TXWD1234/LogicalRedstone/components/redstone-dust/CAD/piece/Redstone Dust - Center.stl

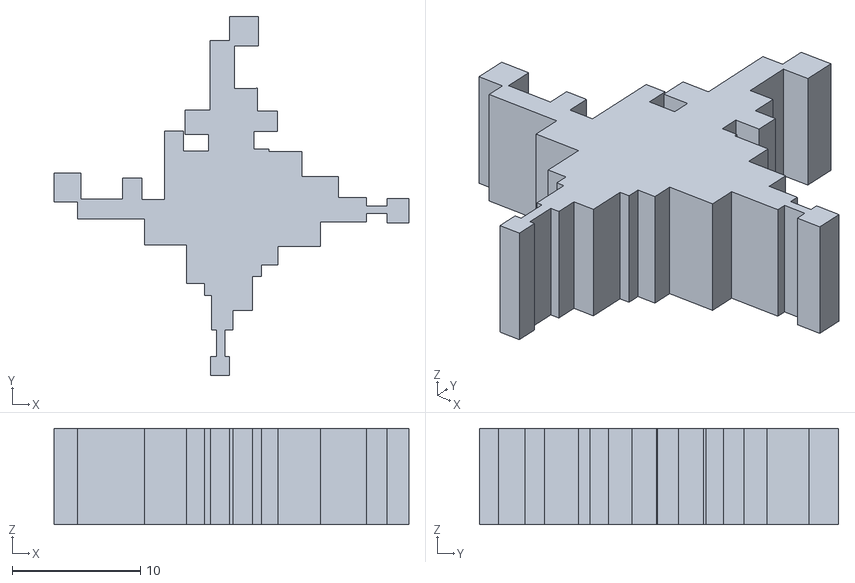
[picture p18: CAD file, 2026-07-06]
components/redstone-dust/CAD/piece/Redstone Dust - Center.stl
27.6 x 28.0 x 7.50
