TXWD1234/LogicalRedstone/components/redstone-button/schematics/redstone-button.kicad_sch

## KiCad design components/redstone-button/schematics/redstone-button.kicad_sch (2026-07-06)

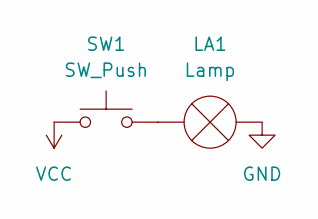
[picture p21: schematic redstone-button.kicad_sch]

Parts:
LA1: Lamp
SW1: SW_Push

Connections:
GND: LA1.1 (-)
unnamed: LA1.2 (+), SW1.2
VCC: SW1.1
