TXWD1234/LogicalRedstone/components/redstone-dust/schematics/redstone-dust-corner.kicad_sch

## KiCad design components/redstone-dust/schematics/redstone-dust-corner.kicad_sch (2026-07-06)

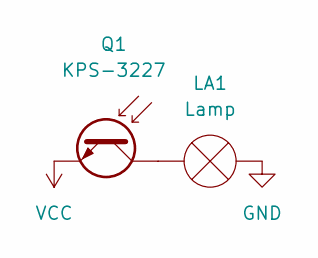
[picture p22: schematic redstone-dust-corner.kicad_sch]

Parts:
LA1: Lamp
Q1: KPS-3227; Kingbright_KPS-3227

Connections:
GND: LA1.1 (-)
unnamed: LA1.2 (+), Q1.1, Q1.3
VCC: Q1.2, Q1.4
