TXWD1234/LogicalRedstone/components/redstone-dust/schematics/redstone-dust-t-junction.kicad_sch

## KiCad design components/redstone-dust/schematics/redstone-dust-t-junction.kicad_sch (2026-07-06)

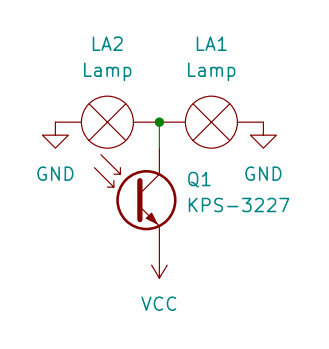
[picture p23: schematic redstone-dust-t-junction.kicad_sch]

Parts:
LA1, LA2: Lamp
Q1: KPS-3227; Kingbright_KPS-3227

Connections:
GND: LA1.1 (-), LA2.1 (-)
unnamed: LA1.2 (+), LA2.2 (+), Q1.1, Q1.3
VCC: Q1.2, Q1.4
