TXWD1234/LogicalRedstone/components/redstone-repeater/schematics/redstone-repeater.kicad_sch

## KiCad design components/redstone-repeater/schematics/redstone-repeater.kicad_sch (2026-07-06)

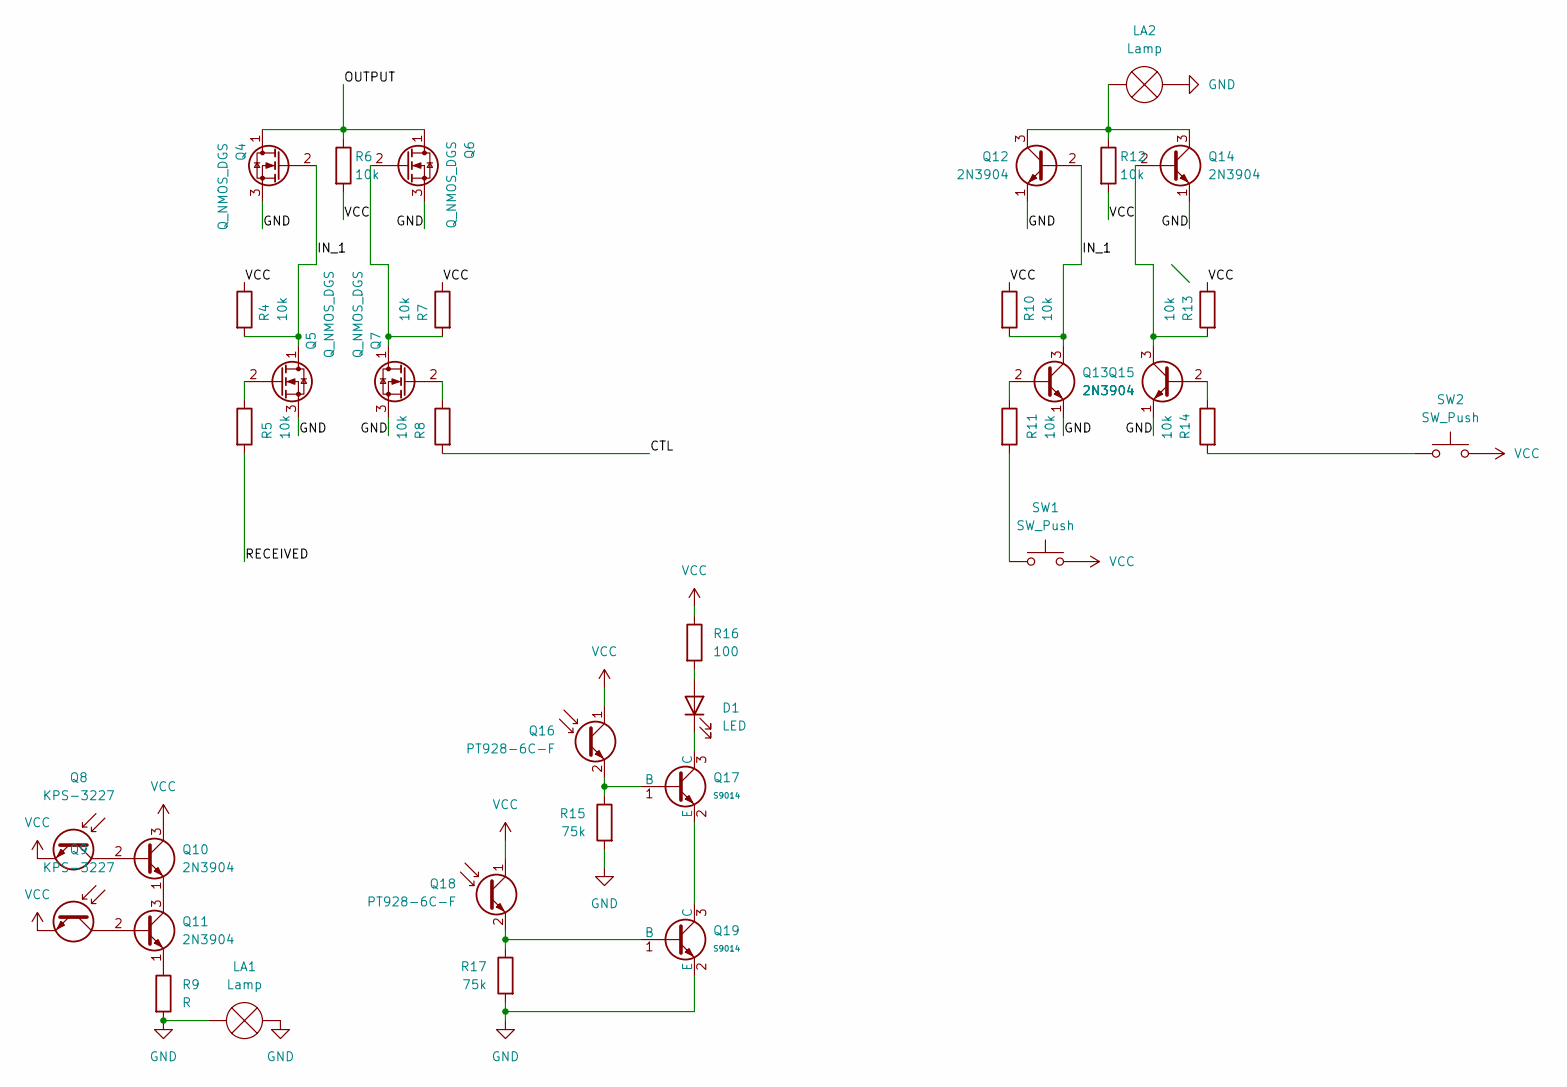
[picture p24: schematic redstone-repeater.kicad_sch]

Parts:
D1: LED
LA1, LA2: Lamp
Q4, Q5, Q6, Q7: Q_NMOS_DGS
Q8, Q9: KPS-3227; Kingbright_KPS-3227
Q10, Q11, Q12, Q13, Q14, Q15: 2N3904; TO-92_Inline
Q16, Q18: PT928-6C-F
Q17, Q19: S9014; Q_SOT-23; Part S9014; LCSC C20069130
R4, R5, R7, R8, R10, R11, R13, R14: 10k; R_Axial_DIN0207_L6.3mm_D2.5mm_P7.62mm_Horizontal
R6, R12: 10k
R9: R
R15, R17: 75k
R16: 100
SW1, SW2: SW_Push

Connections:
CTL: R8.2
GND: LA1.1 (-), LA1.2 (+), LA2.1 (-), Q4.3 (S), Q5.3 (S), Q6.3 (S), Q7.3 (S), Q12.1 (E), Q13.1 (E), Q14.1 (E), Q15.1 (E), Q19.2 (E), R9.2, R15.2, R17.2
IN_1: Q4.2 (G), Q5.1 (D), Q12.2 (B), Q13.3 (C), R4.2, R10.2
unnamed: D1.1 (K), Q17.3 (C)
unnamed: D1.2 (A), R16.2
unnamed: LA2.2 (+), Q12.3 (C), Q14.3 (C), R12.1
unnamed: Q5.2 (G), R5.1
unnamed: Q6.2 (G), Q7.1 (D), R7.2
unnamed: Q7.2 (G), R8.1
unnamed: Q10.1 (E), Q11.3 (C)
unnamed: Q8.1, Q8.3, Q10.2 (B)
unnamed: Q11.1 (E), R9.1
unnamed: Q9.1, Q9.3, Q11.2 (B)
unnamed: Q13.2 (B), R11.1
unnamed: Q14.2 (B), Q15.3 (C), R13.2
unnamed: Q15.2 (B), R14.1
unnamed: Q16.2 (E), Q17.1 (B), R15.1
unnamed: Q17.2 (E), Q19.3 (C)
unnamed: Q18.2 (E), Q19.1 (B), R17.1
unnamed: R11.2, SW1.1
unnamed: R14.2, SW2.1
OUTPUT: Q4.1 (D), Q6.1 (D), R6.1
RECEIVED: R5.2
VCC: Q8.2, Q8.4, Q9.2, Q9.4, Q10.3 (C), Q16.1 (C), Q18.1 (C), R4.1, R6.2, R7.1, R10.1, R12.2, R13.1, R16.1, SW1.2, SW2.2
