TXWD1234/LogicalRedstone/components/redstone-torch/schematics/redstone-torch.kicad_sch

## KiCad design components/redstone-torch/schematics/redstone-torch.kicad_sch (2026-07-06)

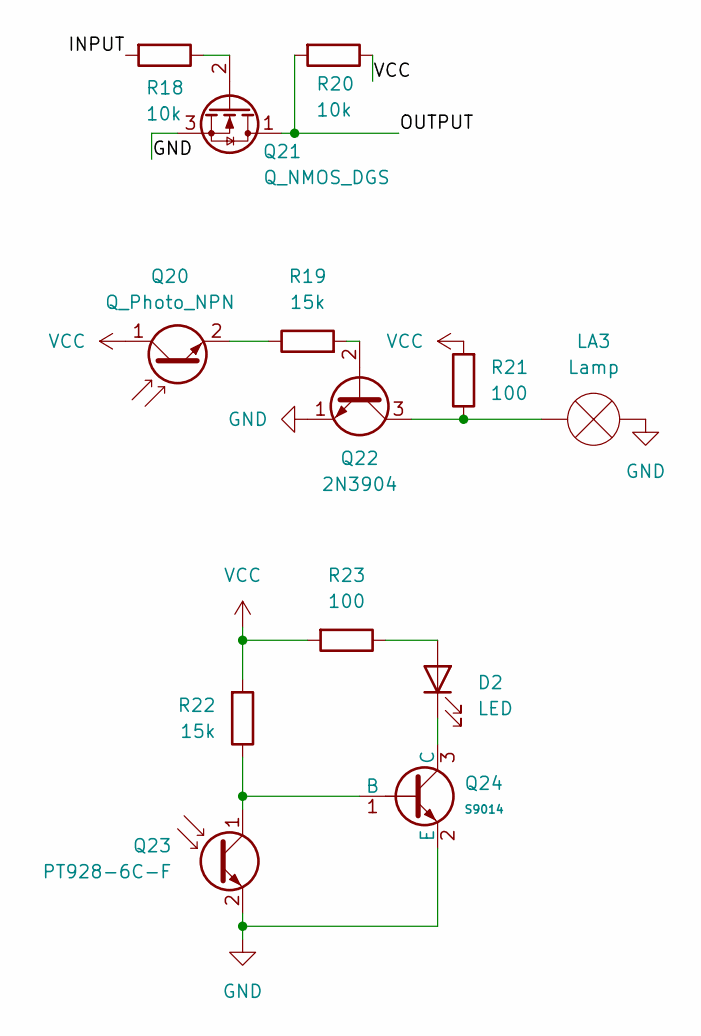
[picture p25: schematic redstone-torch.kicad_sch]

Parts:
D2: LED
LA3: Lamp
Q20: Q_Photo_NPN
Q21: Q_NMOS_DGS
Q22: 2N3904; TO-92_Inline
Q23: PT928-6C-F
Q24: S9014; Q_SOT-23; Part S9014; LCSC C20069130
R18, R20: 10k; R_Axial_DIN0207_L6.3mm_D2.5mm_P7.62mm_Horizontal
R19, R22: 15k
R21, R23: 100

Connections:
GND: LA3.1 (-), Q21.3 (S), Q22.1 (E), Q23.2 (E), Q24.2 (E)
INPUT: R18.2
unnamed: D2.1 (K), Q24.3 (C)
unnamed: D2.2 (A), R23.1
unnamed: LA3.2 (+), Q22.3 (C), R21.1
unnamed: Q20.2 (E), R19.1
unnamed: Q21.2 (G), R18.1
unnamed: Q22.2 (B), R19.2
unnamed: Q23.1 (C), Q24.1 (B), R22.1
OUTPUT: Q21.1 (D), R20.2
VCC: Q20.1 (C), R20.1, R21.2, R22.2, R23.2
