TXWD1234/LogicalRedstone/components/spec/redstone-repeater/redstone-repeater.kicad_sch

## KiCad design components/spec/redstone-repeater/redstone-repeater.kicad_sch (2026-07-05)

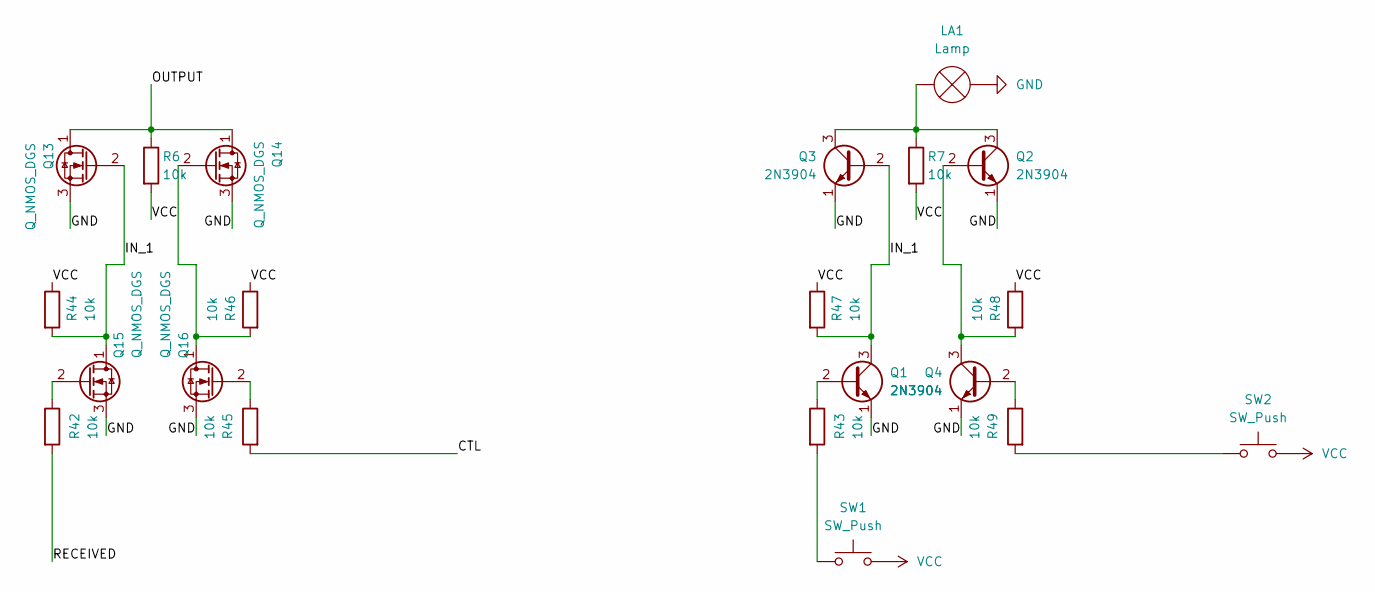
[picture p26: schematic redstone-repeater.kicad_sch]

Parts:
LA1: Lamp
Q1, Q2, Q3, Q4: 2N3904; TO-92_Inline
Q13, Q14, Q15, Q16: Q_NMOS_DGS
R6, R7: 10k
R42, R43, R44, R45, R46, R47, R48, R49: 10k; R_Axial_DIN0207_L6.3mm_D2.5mm_P7.62mm_Horizontal
SW1, SW2: SW_Push

Connections:
CTL: R45.2
GND: LA1.1 (-), Q1.1 (E), Q2.1 (E), Q3.1 (E), Q4.1 (E), Q13.3 (S), Q14.3 (S), Q15.3 (S), Q16.3 (S)
IN_1: Q1.3 (C), Q3.2 (B), Q13.2 (G), Q15.1 (D), R44.2, R47.2
unnamed: LA1.2 (+), Q2.3 (C), Q3.3 (C), R7.1
unnamed: Q1.2 (B), R43.1
unnamed: Q2.2 (B), Q4.3 (C), R48.2
unnamed: Q4.2 (B), R49.1
unnamed: Q14.2 (G), Q16.1 (D), R46.2
unnamed: Q15.2 (G), R42.1
unnamed: Q16.2 (G), R45.1
unnamed: R43.2, SW1.1
unnamed: R49.2, SW2.1
OUTPUT: Q13.1 (D), Q14.1 (D), R6.1
RECEIVED: R42.2
VCC: R6.2, R7.2, R44.1, R46.1, R47.1, R48.1, SW1.2, SW2.2
