TXWD1234/LogicalRedstone/components/spec/redstone-torch/redstone-torch.kicad_sch

## KiCad design components/spec/redstone-torch/redstone-torch.kicad_sch (2026-07-05)

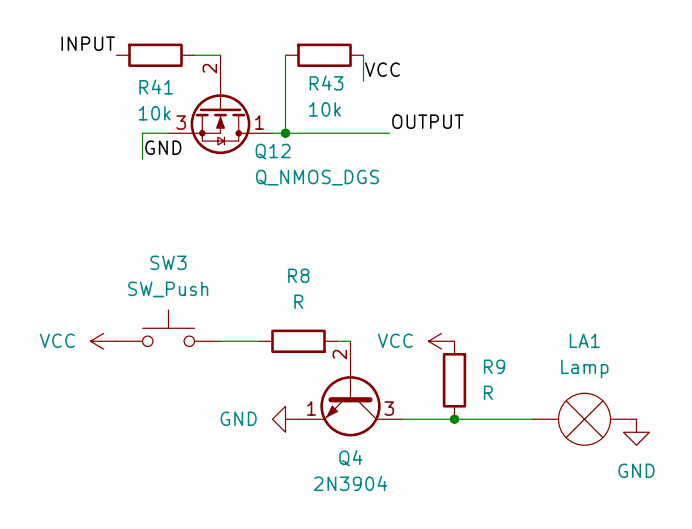
[picture p27: schematic redstone-torch.kicad_sch]

Parts:
LA1: Lamp
Q4: 2N3904; TO-92_Inline
Q12: Q_NMOS_DGS
R8, R9: R
R41, R43: 10k; R_Axial_DIN0207_L6.3mm_D2.5mm_P7.62mm_Horizontal
SW3: SW_Push

Connections:
GND: LA1.1 (-), Q4.1 (E), Q12.3 (S)
INPUT: R41.2
unnamed: LA1.2 (+), Q4.3 (C), R9.1
unnamed: Q4.2 (B), R8.2
unnamed: Q12.2 (G), R41.1
unnamed: R8.1, SW3.2
OUTPUT: Q12.1 (D), R43.2
VCC: R9.2, R43.1, SW3.1
