TXWD1234/LogicalRedstone/demo/adder/schematics/full-adder.kicad_sch

## KiCad design demo/adder/schematics/full-adder.kicad_sch (2026-07-05)

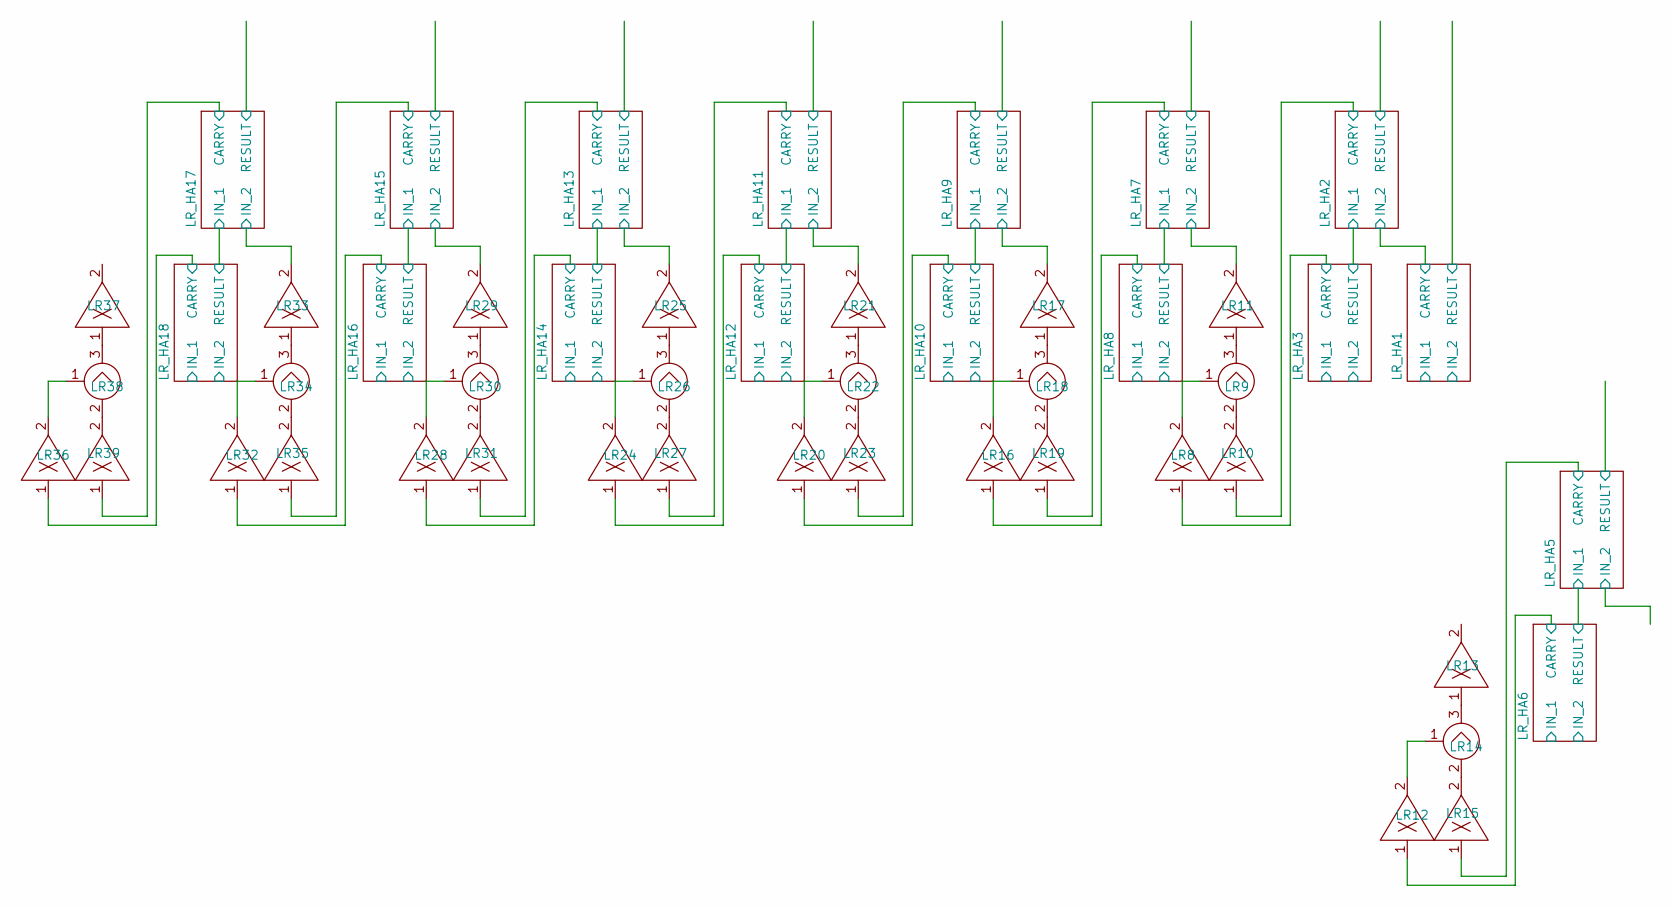
[picture p28: schematic full-adder.kicad_sch]

Parts:
LR8, LR9, LR10, LR11, LR12, LR13, LR14, LR15, LR16, LR17, LR18, LR19, LR20, LR21, LR22, LR23, LR24, LR25, LR26, LR27, LR28, LR29, LR30, LR31, LR32, LR33, LR34, LR35, LR36, LR37, LR38, LR39: (no value)

Connections:
CARRY: LR8.1, LR10.1, LR12.1, LR15.1, LR16.1, LR19.1, LR20.1, LR23.1, LR24.1, LR27.1, LR28.1, LR31.1, LR32.1, LR35.1, LR36.1, LR39.1
IN_2: LR11.2, LR17.2, LR21.2, LR25.2, LR29.2, LR33.2
unnamed: LR8.2, LR9.1
unnamed: LR9.2, LR10.2
unnamed: LR9.3, LR11.1
unnamed: LR12.2, LR14.1
unnamed: LR13.1, LR14.3
unnamed: LR14.2, LR15.2
unnamed: LR16.2, LR18.1
unnamed: LR17.1, LR18.3
unnamed: LR18.2, LR19.2
unnamed: LR20.2, LR22.1
unnamed: LR21.1, LR22.3
unnamed: LR22.2, LR23.2
unnamed: LR24.2, LR26.1
unnamed: LR25.1, LR26.3
unnamed: LR26.2, LR27.2
unnamed: LR28.2, LR30.1
unnamed: LR29.1, LR30.3
unnamed: LR30.2, LR31.2
unnamed: LR32.2, LR34.1
unnamed: LR33.1, LR34.3
unnamed: LR34.2, LR35.2
unnamed: LR36.2, LR38.1
unnamed: LR37.1, LR38.3
unnamed: LR38.2, LR39.2
