TXWD1234/LogicalRedstone/demo/adder/schematics/half-adder.kicad_sch

## KiCad design demo/adder/schematics/half-adder.kicad_sch (2026-07-05)

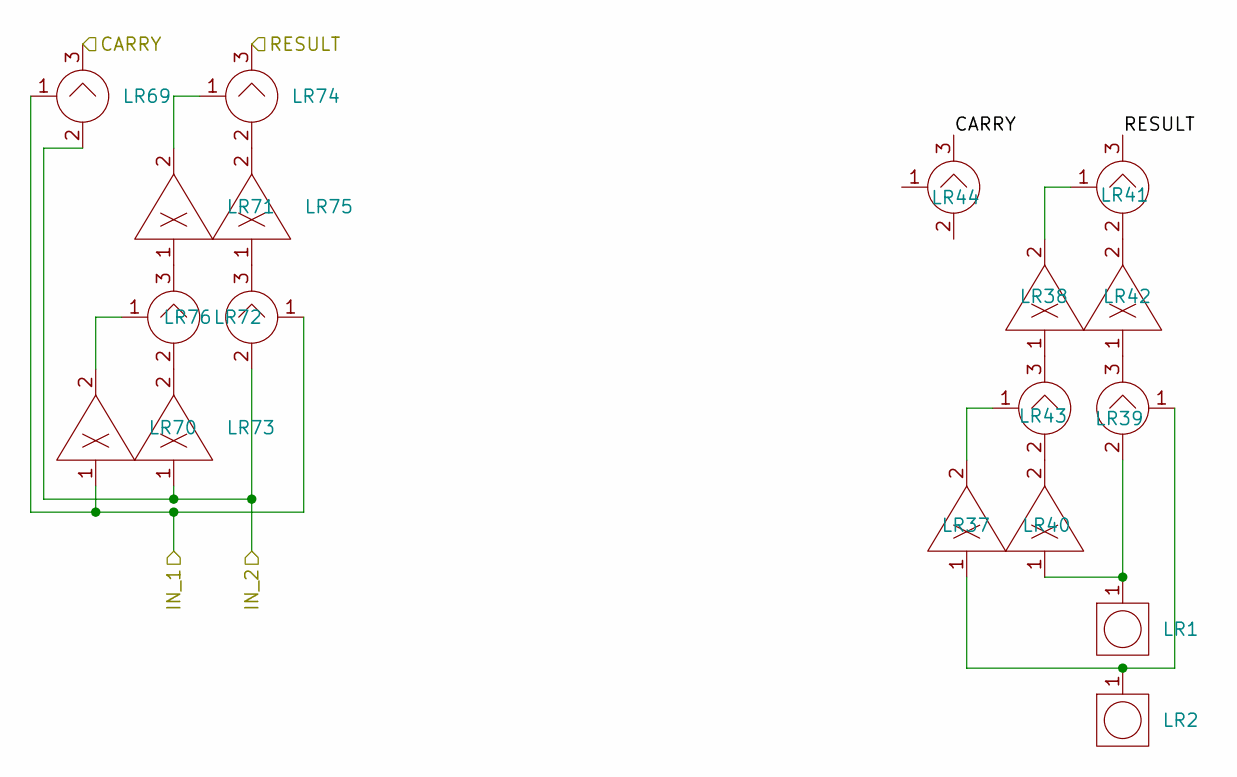
[picture p29: schematic half-adder.kicad_sch]

Parts:
LR1, LR2, LR37, LR38, LR39, LR40, LR41, LR42, LR43, LR44, LR69, LR70, LR71, LR72, LR73, LR74, LR75, LR76: (no value)

Connections:
CARRY: LR44.3, LR69.3
IN_1: LR69.1, LR70.1, LR76.1
IN_2: LR69.2, LR73.1, LR76.2
unnamed: LR1.1, LR40.1, LR43.2
unnamed: LR2.1, LR37.1, LR43.1
unnamed: LR37.2, LR39.1
unnamed: LR38.1, LR39.3
unnamed: LR38.2, LR41.1
unnamed: LR39.2, LR40.2
unnamed: LR41.2, LR42.2
unnamed: LR42.1, LR43.3
unnamed: LR70.2, LR72.1
unnamed: LR71.1, LR72.3
unnamed: LR71.2, LR74.1
unnamed: LR72.2, LR73.2
unnamed: LR74.2, LR75.2
unnamed: LR75.1, LR76.3
RESULT: LR41.3, LR74.3
